Laser4DIY/XY-Table/2mm_EndPlateUpper_OuterPart.dxf

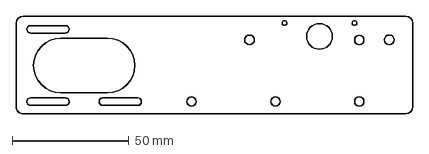
[picture p17: CAD file, 2021-02-19]
2mm_EndPlateUpper_OuterPart.dxf
170.0 x 41.9 mm
