Laser4DIY/XY-Table/2mm_EndPlateUpper_BeamBracket.dxf

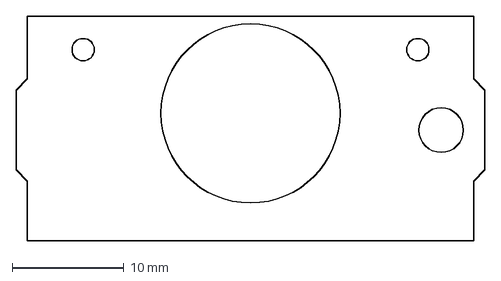
[picture p18: CAD file, 2021-02-19]
2mm_EndPlateUpper_BeamBracket.dxf
42.0 x 20.1 mm
