Laser4DIY/XY-Table/2mm_ALL_with_tabs.dxf

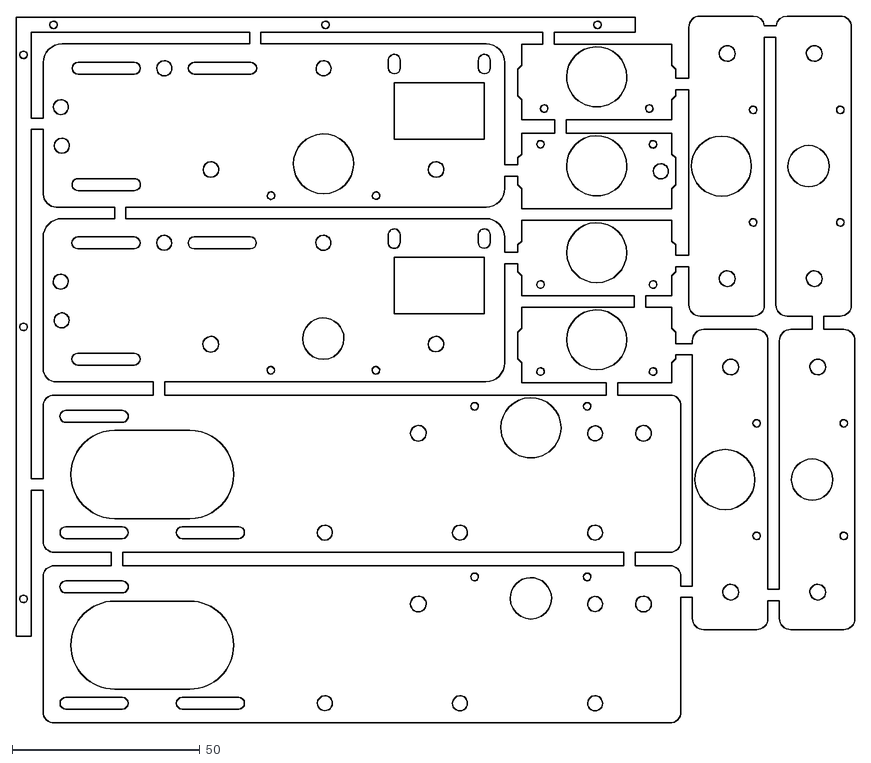
[picture p19: CAD file, 2021-02-19]
2mm_ALL_with_tabs.dxf
223.6 x 188.4
