Laser4DIY/XY-Table/2mm_StandardEndPlate_OuterPart.dxf

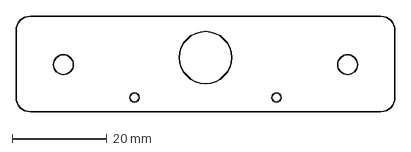
[picture p20: CAD file, 2021-02-19]
2mm_StandardEndPlate_OuterPart.dxf
80.0 x 20.1 mm
